mhendriks/DSMR-API-V2/.github/images/v3.1-eindresultaat.jpg

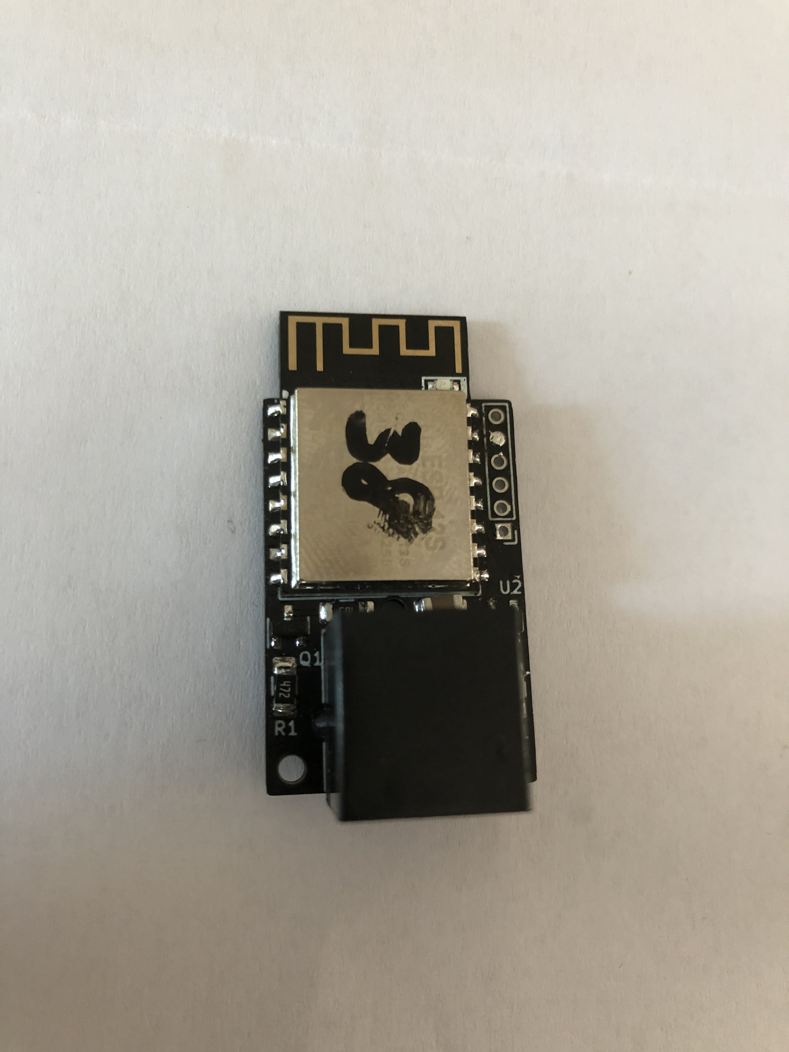
.github/images/v3.1-eindresultaat.jpg
