mhendriks/DSMR-API-V2/.github/images/v3.1-kicad-schema.png

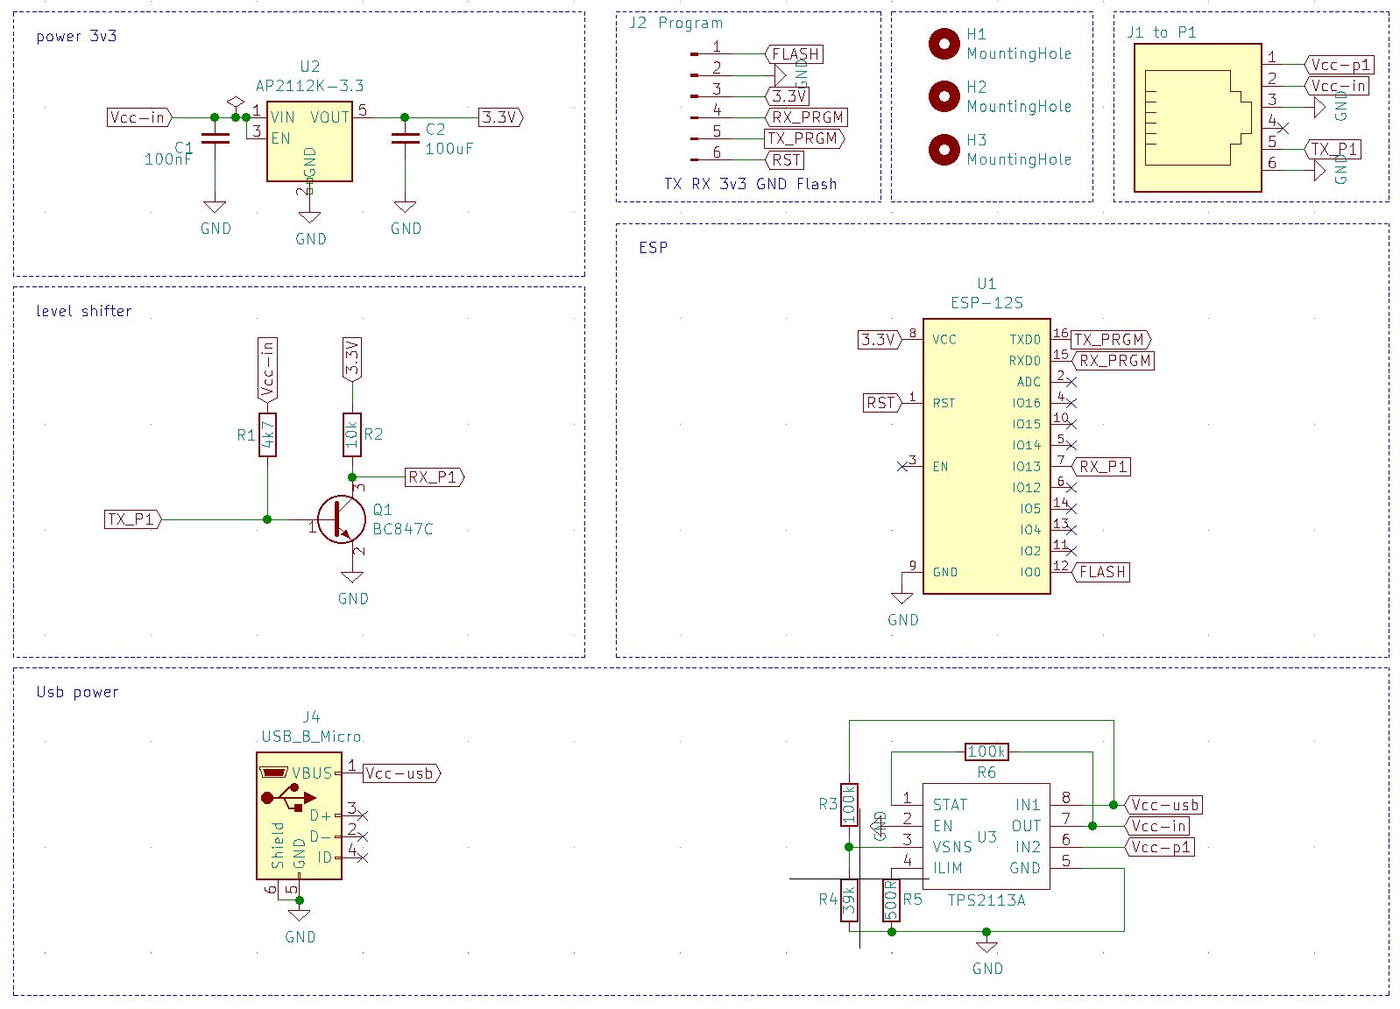
.github/images/v3.1-kicad-schema.png
