mhendriks/DSMR-API-V2/.github/images/v3.3-kicad-schema.png

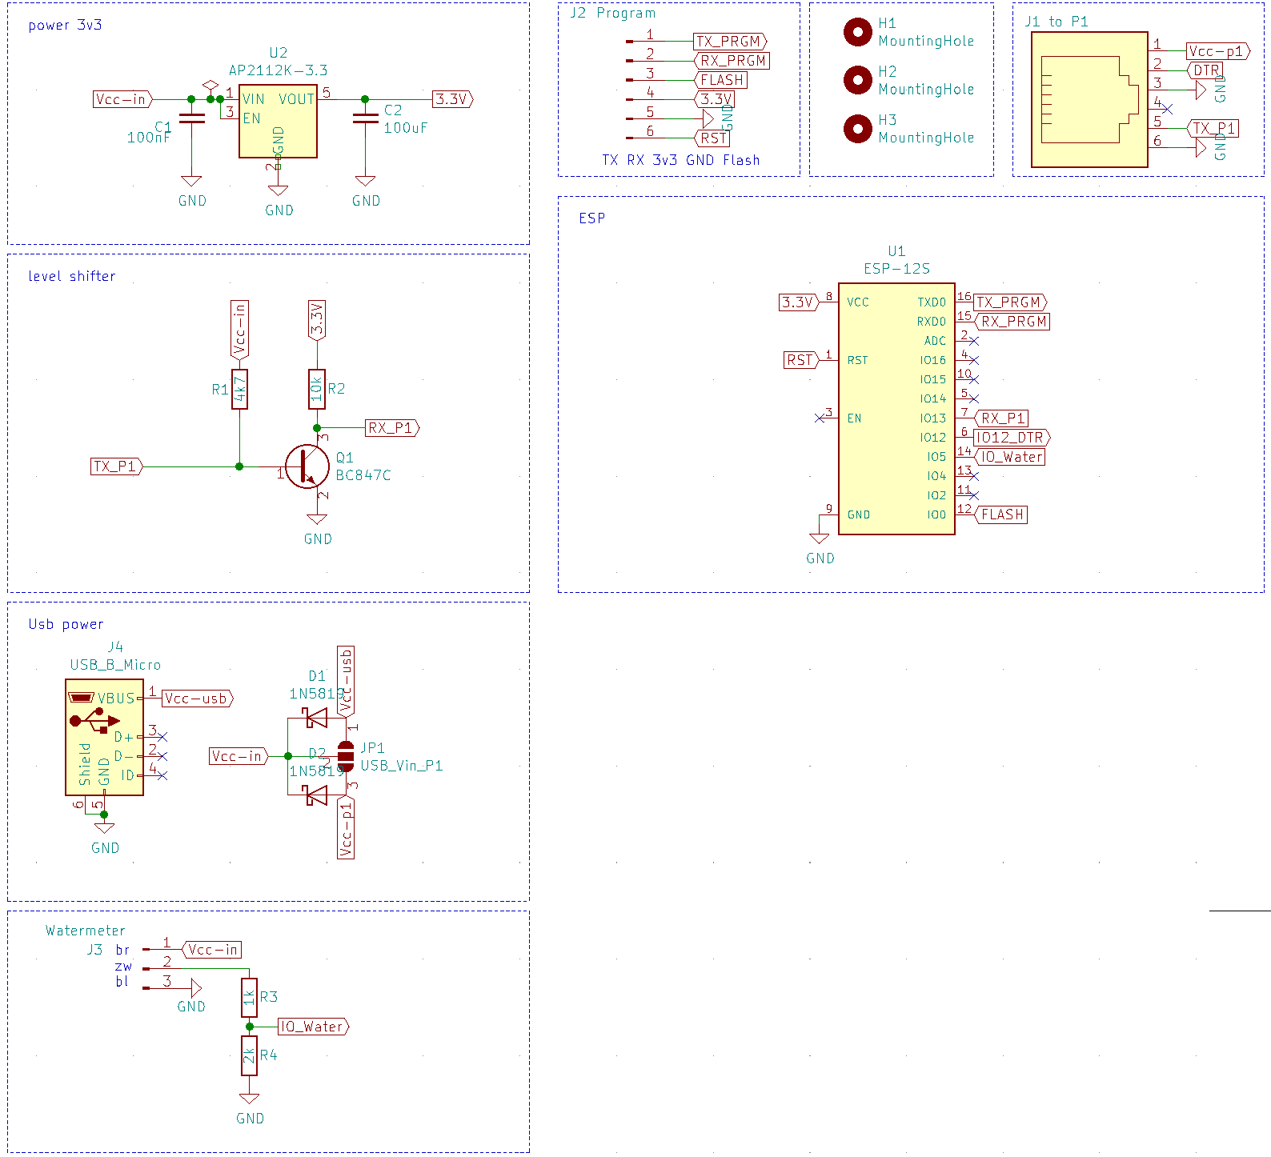
.github/images/v3.3-kicad-schema.png
