mhendriks/DSMR-API-V2/manual/dsmr-api/afb/afbeelding3a.png

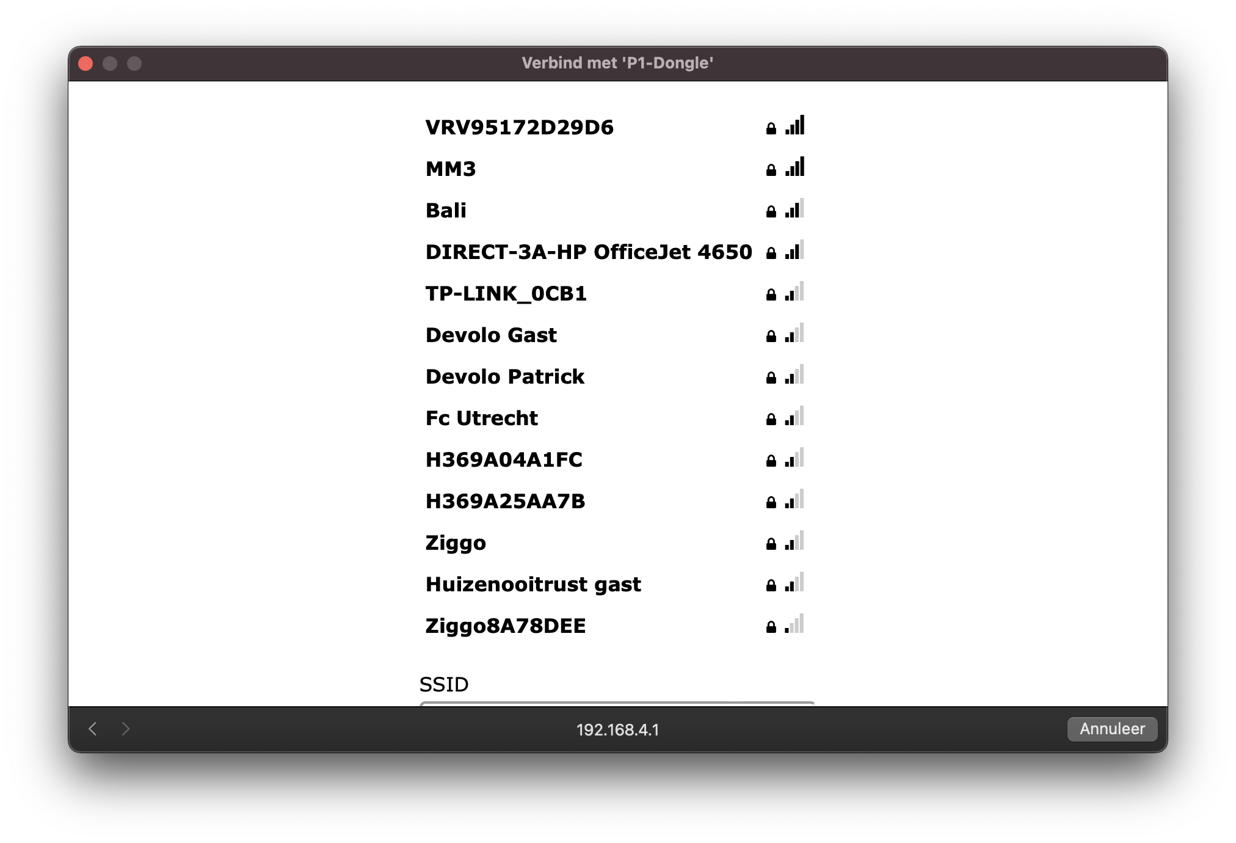
manual/dsmr-api/afb/afbeelding3a.png
