mhendriks/DSMR-API-V2/manual/dsmr-api/afb/check-ip.png

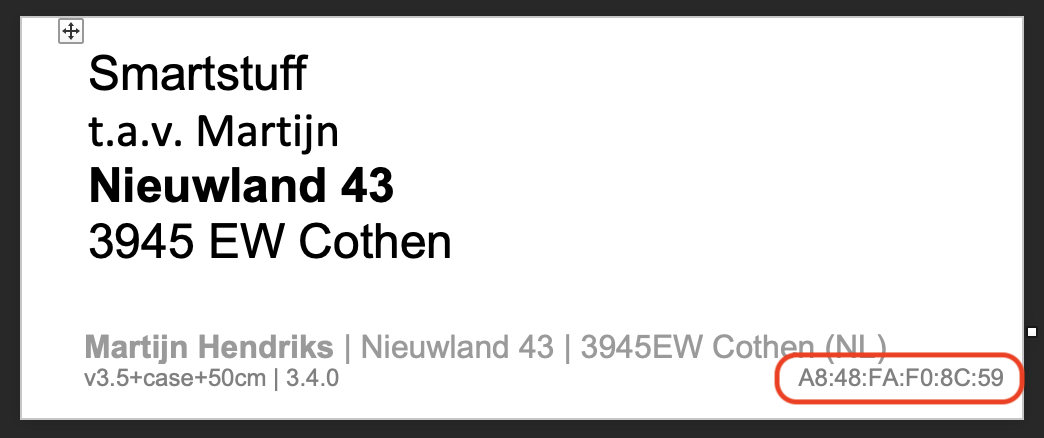
manual/dsmr-api/afb/check-ip.png
