mhendriks/DSMR-API-V2/manual/dsmr-api/Blynk/blynk-app.png

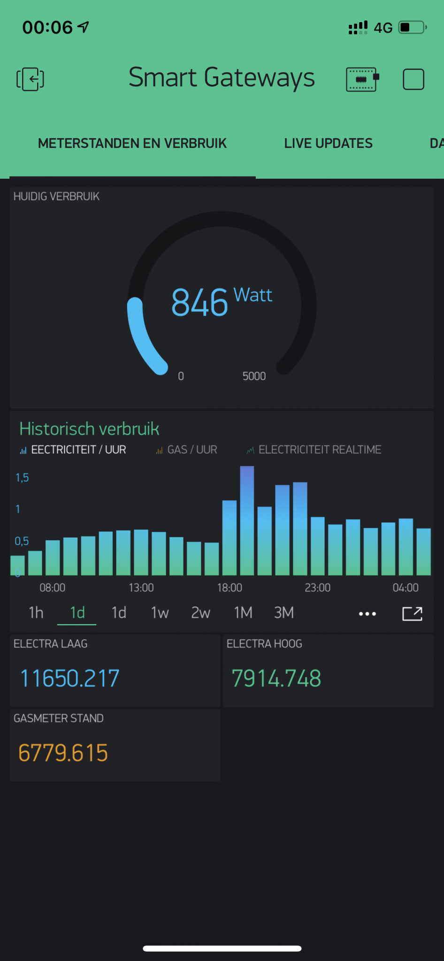
manual/dsmr-api/Blynk/blynk-app.png
