mhendriks/DSMR-API-V2/manual/dsmr-api/watermeter/afb/v4.2-boven.png

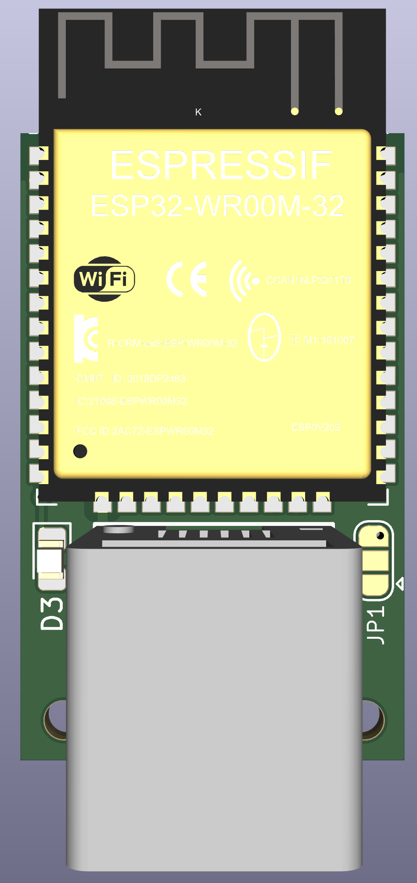
manual/dsmr-api/watermeter/afb/v4.2-boven.png
