mhendriks/DSMR-API-V2/MQTT.ino

/* 
***************************************************************************  
**  Program  : MQTT, part of DSMRloggerAPI
**  Version  : v3.0.0
**
**  Copyright (c) 2021 Willem Aandewiel / Martijn Hendriks  
**
**  TERMS OF USE: MIT License. See bottom of file.                                                            
***************************************************************************      
**  RvdB  changed MQTT stuff to FSM 
**  AaW   simplified and restructured the FSM 
*/

// Declare some variables within global scope

  static IPAddress    MQTTbrokerIP;
  static char         MQTTbrokerIPchar[20];
  int8_t              reconnectAttempts = 0;
  char                lastMQTTtimestamp[15] = "-";
  char                mqttBuff[100];

  enum states_of_MQTT { MQTT_STATE_INIT, MQTT_STATE_TRY_TO_CONNECT, MQTT_STATE_IS_CONNECTED, MQTT_STATE_ERROR };
  enum states_of_MQTT stateMQTT = MQTT_STATE_INIT;

  String            MQTTclientId;

#ifdef HA_DISCOVER
/*

void SendAutoDiscoverHA(const char* dev_name, const char* dev_class, const char* dev_title, const char* dev_unit, const char* dev_payload, const char* state_class, const char* extrapl ){
  char msg_topic[75];
  char msg_payload[500];
  sprintf(msg_topic,"homeassistant/sensor/p1-dongle/%s/config",dev_name);
//    Debugln(msg_topic);

  if (strlen(dev_class)) sprintf(msg_payload,"{\"uniq_id\":\"%s\",\"dev_cla\": \"%s\",\"name\": \"%s\", \"stat_t\": \"%s%s\", \"unit_of_meas\": \"%s\", \"val_tpl\": \"%s\", \"state_class\":\"%s\"%s }", dev_name,dev_class, dev_title, settingMQTTtopTopic, dev_name, dev_unit, dev_payload,state_class, extrapl);
  else sprintf(msg_payload,"{\"uniq_id\":\"%s\",\"name\": \"%s\", \"stat_t\": \"%s%s\", \"unit_of_meas\": \"%s\", \"val_tpl\": \"%s\", \"state_class\":\"%s\"%s }", dev_name, dev_title, settingMQTTtopTopic, dev_name, dev_unit, dev_payload,state_class, extrapl);
//    Debugln(msg_payload);
    if (!MQTTclient.publish(msg_topic, msg_payload, true) ) DebugTf("Error publish(%s) [%s] [%d bytes]\r\n", msg_topic, msg_payload, (strlen(msg_topic) + strlen(msg_payload)));
}

void AutoDiscoverHA(){
//mosquitto_pub -h 192.168.2.250 -p 1883 -t "homeassistant/sensor/power_delivered/config" -m '{"dev_cla": "gas", "name": "Power Delivered", "stat_t": "DSMR-API/power_delivered", "unit_of_meas": "Wh", "val_tpl": "{{ value_json.power_delivered[0].value | round(3) }}" }'

  SendAutoDiscoverHA("timestamp", "", "DSMR Last Update", "", "{{ strptime(value_json.timestamp[0].value[0:12], \'%y%m%d%H%M%S\') }}","measurement", ",\"icon\": \"mdi:clock\"");
  
  SendAutoDiscoverHA("power_delivered", "power", "Power Delivered", "W", "{{ value_json.power_delivered[0].value | round(3) * 1000}}","measurement","");
  SendAutoDiscoverHA("power_returned", "power", "Power Returned", "W", "{{ value_json.power_returned[0].value | round(3) * 1000}}","measurement","");  
  
  SendAutoDiscoverHA("energy_delivered_tariff1", "energy", "Energy Delivered T1", "kWh", "{{ value_json.energy_delivered_tariff1[0].value | round(3) }}","total_increasing","");
  SendAutoDiscoverHA("energy_delivered_tariff2", "energy", "Energy Delivered T2", "kWh", "{{ value_json.energy_delivered_tariff2[0].value | round(3) }}","total_increasing","");
  SendAutoDiscoverHA("energy_returned_tariff1", "energy", "Energy Returned T1", "kWh", "{{ value_json.energy_returned_tariff1[0].value | round(3) }}","total_increasing","");
  SendAutoDiscoverHA("energy_returned_tariff2", "energy", "Energy Returned T2", "kWh", "{{ value_json.energy_returned_tariff2[0].value | round(3) }}","total_increasing","");
  
  SendAutoDiscoverHA("power_delivered_l1", "power", "Power Delivered l1", "W", "{{ value_json.power_delivered_l1[0].value | round(3) * 1000 }}","measurement","");
  SendAutoDiscoverHA("power_delivered_l2", "power", "Power Delivered l2", "W", "{{ value_json.power_delivered_l2[0].value | round(3) * 1000 }}","measurement","");
  SendAutoDiscoverHA("power_delivered_l3", "power", "Power Delivered l3", "W", "{{ value_json.power_delivered_l3[0].value | round(3) * 1000 }}","measurement","");

  SendAutoDiscoverHA("power_returned_l1", "power", "Power Returned l1", "W", "{{ value_json.power_returned_l1[0].value | round(3) * 1000 }}","measurement","");
  SendAutoDiscoverHA("power_returned_l2", "power", "Power Returned l2", "W", "{{ value_json.power_returned_l2[0].value | round(3) * 1000 }}","measurement","");
  SendAutoDiscoverHA("power_returned_l3", "power", "Power Returned l3", "W", "{{ value_json.power_returned_l3[0].value | round(3) * 1000 }}","measurement","");

  SendAutoDiscoverHA("voltage_l1", "voltage", "Voltage l1", "V", "{{ value_json.voltage_l1[0].value | round(0) }}","measurement","");
  SendAutoDiscoverHA("voltage_l2", "voltage", "Voltage l2", "V", "{{ value_json.voltage_l2[0].value | round(0) }}","measurement","");
  SendAutoDiscoverHA("voltage_l3", "voltage", "Voltage l3", "V", "{{ value_json.voltage_l3[0].value | round(0) }}","measurement","");
  
  SendAutoDiscoverHA("current_l1", "current", "Current l1", "A", "{{ value_json.current_l1[0].value | round(0) }}","measurement","");
  SendAutoDiscoverHA("current_l2", "current", "Current l2", "A", "{{ value_json.current_l2[0].value | round(0) }}","measurement","");
  SendAutoDiscoverHA("current_l3", "current", "Current l3", "A", "{{ value_json.current_l3[0].value | round(0) }}","measurement","");

  SendAutoDiscoverHA("gas_delivered", "gas", "Gas Delivered", "m³", "{{ value_json.gas_delivered[0].value | round(2) }}","total_increasing","");
    
}
*/


//--- NEW
String AddPayload(const char* key, const char* value ){
  if ( strlen(value) == 0 ) return "";
  return "\"" + String(key) + "\":\"" + String(value) + "\",";
}

void SendAutoDiscoverHA(const char* dev_name, const char* dev_class, const char* dev_title, const char* dev_unit, const char* dev_payload, const char* state_class, const char* extrapl ){
  char msg_topic[80];
  String msg_payload = "{";
  sprintf(msg_topic,"homeassistant/sensor/p1-dongle/%s/config",dev_name);
//    Debugln(msg_topic);
  msg_payload += AddPayload( "uniq_id"        , dev_name);
  msg_payload += AddPayload( "dev_cla"        , dev_class);
  msg_payload += AddPayload( "name"           , dev_title);
  msg_payload += AddPayload( "stat_t"         , String((String)settingMQTTtopTopic + (String)dev_name).c_str() );
  msg_payload += AddPayload( "unit_of_meas"   , dev_unit);
  msg_payload += AddPayload( "val_tpl"        , dev_payload);
  msg_payload += AddPayload( "stat_cla"       , state_class);
  msg_payload += extrapl;
  msg_payload += "\"dev\":{";
  msg_payload += AddPayload("ids"             , String(WIFI_getChipId()).c_str() );
  msg_payload += AddPayload("name"            , settingHostname);
  msg_payload += "\"mdl\":\"P1 Dongle\",\"mf\":\"Smartstuff\"}}";
//  Debugln(msg_payload);
  if (!MQTTclient.publish(msg_topic, msg_payload.c_str(), true) ) DebugTf("Error publish(%s) [%s] [%d bytes]\r\n", msg_topic, msg_payload, ( strlen(msg_topic) + msg_payload.length() ));
}

void AutoDiscoverHA(){
//mosquitto_pub -h 192.168.2.250 -p 1883 -t "homeassistant/sensor/power_delivered/config" -m '{"dev_cla": "gas", "name": "Power Delivered", "stat_t": "DSMR-API/power_delivered", "unit_of_meas": "Wh", "val_tpl": "{{ value_json.power_delivered[0].value | round(3) }}" }'

  SendAutoDiscoverHA("timestamp", "timestamp", "DSMR Last Update", "", "{{ strptime(value_json.timestamp[0].value[:-1] + '-+0200' if value_json.timestamp[0].value[12] == 'S' else value_json.timestamp[0].value[:-1] + '-+0100', '%y%m%d%H%M%S-%z') }}","", "\"icon\": \"mdi:clock\",");
  SendAutoDiscoverHA("power_delivered", "power", "Power Delivered", "W", "{{ value_json.power_delivered[0].value | round(3) * 1000 }}","measurement","");
  SendAutoDiscoverHA("power_returned" , "power", "Power Returned" , "W", "{{ value_json.power_returned[0].value | round(3) * 1000 }}","measurement","");  
  
  SendAutoDiscoverHA("energy_delivered_tariff1", "energy", "Energy Delivered T1", "kWh", "{{ value_json.energy_delivered_tariff1[0].value | round(3) }}","total_increasing","");
  SendAutoDiscoverHA("energy_delivered_tariff2", "energy", "Energy Delivered T2", "kWh", "{{ value_json.energy_delivered_tariff2[0].value | round(3) }}","total_increasing","");
  SendAutoDiscoverHA("energy_returned_tariff1", "energy", "Energy Returned T1", "kWh", "{{ value_json.energy_returned_tariff1[0].value | round(3) }}","total_increasing","");
  SendAutoDiscoverHA("energy_returned_tariff2", "energy", "Energy Returned T2", "kWh", "{{ value_json.energy_returned_tariff2[0].value | round(3) }}","total_increasing","");
  
  SendAutoDiscoverHA("power_delivered_l1", "power", "Power Delivered l1", "W", "{{ value_json.power_delivered_l1[0].value | round(3) * 1000 }}","measurement","");
  SendAutoDiscoverHA("power_delivered_l2", "power", "Power Delivered l2", "W", "{{ value_json.power_delivered_l2[0].value | round(3) * 1000 }}","measurement","");
  SendAutoDiscoverHA("power_delivered_l3", "power", "Power Delivered l3", "W", "{{ value_json.power_delivered_l3[0].value | round(3) * 1000 }}","measurement","");

  SendAutoDiscoverHA("power_returned_l1", "power", "Power Returned l1", "W", "{{ value_json.power_returned_l1[0].value | round(3) * 1000 }}","measurement","");
  SendAutoDiscoverHA("power_returned_l2", "power", "Power Returned l2", "W", "{{ value_json.power_returned_l2[0].value | round(3) * 1000 }}","measurement","");
  SendAutoDiscoverHA("power_returned_l3", "power", "Power Returned l3", "W", "{{ value_json.power_returned_l3[0].value | round(3) * 1000 }}","measurement","");

  SendAutoDiscoverHA("voltage_l1", "voltage", "Voltage l1", "V", "{{ value_json.voltage_l1[0].value | round(0) }}","measurement","");
  SendAutoDiscoverHA("voltage_l2", "voltage", "Voltage l2", "V", "{{ value_json.voltage_l2[0].value | round(0) }}","measurement","");
  SendAutoDiscoverHA("voltage_l3", "voltage", "Voltage l3", "V", "{{ value_json.voltage_l3[0].value | round(0) }}","measurement","");
  
  SendAutoDiscoverHA("current_l1", "current", "Current l1", "A", "{{ value_json.current_l1[0].value | round(0) }}","measurement","");
  SendAutoDiscoverHA("current_l2", "current", "Current l2", "A", "{{ value_json.current_l2[0].value | round(0) }}","measurement","");
  SendAutoDiscoverHA("current_l3", "current", "Current l3", "A", "{{ value_json.current_l3[0].value | round(0) }}","measurement","");

  SendAutoDiscoverHA("gas_delivered", "gas", "Gas Delivered", "m³", "{{ value_json.gas_delivered[0].value | round(2) }}","total_increasing","");
  
}
#endif

//===========================================================================================
void connectMQTT() 
{
  
  if (Verbose2) DebugTf("MQTTclient.connected(%d), mqttIsConnected[%d], stateMQTT [%d]\r\n", MQTTclient.connected(), mqttIsConnected, stateMQTT);

  if ( (settingMQTTinterval == 0) || (strlen(settingMQTTbroker) < 4) ) {
    mqttIsConnected = false;
    return;
  }
  
  if (!MQTTclient.connected() || stateMQTT != MQTT_STATE_IS_CONNECTED)
  {
    mqttIsConnected = false;
    stateMQTT = MQTT_STATE_INIT;
  }

  mqttIsConnected = connectMQTT_FSM();
  
  if (Verbose1) DebugTf("connected()[%d], mqttIsConnected[%d], stateMQTT [%d]\r\n", MQTTclient.connected(), mqttIsConnected, stateMQTT);

  CHANGE_INTERVAL_SEC(reconnectMQTTtimer, 5);

}

//===========================================================================================

void MQTTcallback(char* topic, byte* payload, unsigned int length) {
  if (length > 24) return;
  for (int i=0;i<length;i++) UpdateVersion[i] = (char)payload[i];
  DebugT(F("Message arrived ["));Debug(topic);Debug("] ");Debugln(UpdateVersion);
  UpdateRequested = true;
}

//===========================================================================================
bool connectMQTT_FSM() 
{  
  switch(stateMQTT) 
  {
    case MQTT_STATE_INIT:  
//          DebugTln(F("MQTT State: MQTT Initializing"));
          LogFile("MQTT State: MQTT Initializing",true);
          WiFi.hostByName(settingMQTTbroker, MQTTbrokerIP);  // lookup the MQTTbroker convert to IP
/*
int n = MDNS.queryService("espserver", "tcp");
 
  if (n == 0)  DebugTln("No MQTT host found");
  else {
    Serial.println("Service found");
    Serial.println("Host: " + String(MDNS.hostname(0)));
    Serial.print("IP  : " );
    Serial.println(MDNS.IP(0));
    Serial.println("Port: " + String(MDNS.port(0)));
  }
*/   
          snprintf(MQTTbrokerIPchar, sizeof(MQTTbrokerIPchar), "%d.%d.%d.%d", MQTTbrokerIP[0]
                                                                            , MQTTbrokerIP[1]
                                                                            , MQTTbrokerIP[2]
                                                                            , MQTTbrokerIP[3]);
          if (!isValidIP(MQTTbrokerIP))  
          {
            DebugTf("ERROR: [%s] => is not a valid URL\r\n", settingMQTTbroker);
            settingMQTTinterval = 0;
            stateMQTT = MQTT_STATE_ERROR;
            return false;
          }
          
          //MQTTclient.disconnect();
          //DebugTf("disconnect -> MQTT status, rc=%d \r\n", MQTTclient.state());
          DebugTf("[%s] => setServer(%s, %d) \r\n", settingMQTTbroker, MQTTbrokerIPchar, settingMQTTbrokerPort);
          MQTTclient.setServer(MQTTbrokerIPchar, settingMQTTbrokerPort);
          DebugTf("setServer  -> MQTT status, rc=%d \r\n", MQTTclient.state());
          MQTTclientId  = String(settingHostname) + "-" + WiFi.macAddress();
          MQTTclient.setCallback(MQTTcallback); //set listner update callback
          stateMQTT = MQTT_STATE_TRY_TO_CONNECT;
          reconnectAttempts = 0;

    case MQTT_STATE_TRY_TO_CONNECT:
          LogFile("MQTT State: MQTT try to connect",true);
          DebugTf("MQTT server is [%s], IP[%s]\r\n", settingMQTTbroker, MQTTbrokerIPchar);
      
          DebugTf("Attempting MQTT connection as [%s] .. \r\n", MQTTclientId.c_str());
          reconnectAttempts++;

          //--- If no username, then anonymous connection to broker, otherwise assume username/password.
          sprintf(cMsg,"%sLWT",settingMQTTtopTopic);
          if (String(settingMQTTuser).length() == 0) 
          {
            DebugT(F("without a Username/Password "));
            MQTTclient.connect(MQTTclientId.c_str(),"","",cMsg,1,true,"Offline");
          } 
          else 
          {
            DebugTf("with Username [%s] and password ", settingMQTTuser);
            MQTTclient.connect(MQTTclientId.c_str(), settingMQTTuser, settingMQTTpasswd,cMsg,1,true,"Offline");
          }
          //--- If connection was made succesful, move on to next state...
          if (MQTTclient.connected())
          {
            reconnectAttempts = 0;  
            Debugf(" .. connected -> MQTT status, rc=%d\r\n", MQTTclient.state());
            MQTTclient.publish(cMsg,"Online", true);
            sprintf(cMsg,"%supdate",settingMQTTtopTopic);
            MQTTclient.setBufferSize(650);
#ifdef HA_DISCOVER
            AutoDiscoverHA();
#endif            
            MQTTclient.subscribe(cMsg); //subscribe mqtt update

            LogFile("MQTT connected",false);
            MQTTclient.loop();
            stateMQTT = MQTT_STATE_IS_CONNECTED;
            return true;
          }
          Debugf(" -> MQTT status, rc=%d \r\n", MQTTclient.state());
      
          //--- After 3 attempts... go wait for a while.
          if (reconnectAttempts >= 3)
          {
            DebugTln(F("3 attempts have failed. Retry wait for next reconnect in 5 secs\r"));
            stateMQTT = MQTT_STATE_ERROR;  // if the re-connect did not work, then return to wait for reconnect
            DebugTln(F("Next State: MQTT_STATE_ERROR"));
          }   
          break;
          
    case MQTT_STATE_IS_CONNECTED:
          LogFile("MQTT Connected",false);
          MQTTclient.loop();
          return true;

    case MQTT_STATE_ERROR:
          LogFile("MQTT Error: retry in 5 seconds",true);

          //--- next retry in 5 sec.
          CHANGE_INTERVAL_SEC(reconnectMQTTtimer, 5);
          break;

    default:
          DebugTln(F("MQTT State: default, this should NEVER happen!"));
          //--- do nothing, this state should not happen
          stateMQTT = MQTT_STATE_INIT;
          CHANGE_INTERVAL_SEC(reconnectMQTTtimer, 5);
          DebugTln(F("Next State: MQTT_STATE_INIT"));
          break;
  }

  return false;  

} // connectMQTT_FSM()

//=======================================================================
void MQTTsendGas(){

  if (gasDelivered){
    sprintf(cMsg,"%s%s",settingMQTTtopTopic,"gas_delivered");
    char msg[60];
    sprintf(msg,"{\"gas_delivered\":[{\"value\":%.3f,\"unit\":\"m3\"}]}",gasDelivered);
    if (!MQTTclient.publish(cMsg, msg) ) DebugTf("Error publish(%s) [%s] [%d bytes]\r\n", cMsg, msg, (strlen(cMsg) + strlen(msg)));
  }
}

//=======================================================================
void MQTTsendWater(){

  if (waterDelivered){
    sprintf(cMsg,"%s%s",settingMQTTtopTopic,"water_delivered");
    char msg[60];
    sprintf(msg,"{\"water_delivered\":[{\"value\":%.3f,\"unit\":\"m3\"}]}",waterDelivered);
    if (!MQTTclient.publish(cMsg, msg) ) DebugTf("Error publish(%s) [%s] [%d bytes]\r\n", cMsg, msg, (strlen(cMsg) + strlen(msg)));
  }
}
//=======================================================================

struct buildJsonMQTT {
/* twee types
 *  {energy_delivered_tariff1":[{"value":11741.29,"unit":"kWh"}]}"
 *  {equipment_id":[{"value":"4530303435303033383833343439383137"}]}"
 *  
 *  msg = "{\""+Name+"\":[{\"value\":"+value_to_json(i.val())+",\"unit\":"+Unit+"}]}";
 *  msg = "\"{\""+Name+"\":[{\"value\":"+value_to_json(i.val())+"}]}\""
 *  
 */
     char msg[256];  
    template<typename Item>
    void apply(Item &i) {
      char Name[25];
      strncpy(Name,String(Item::name).c_str(),sizeof(Name));
      if ( !isInFieldsArray(Name) ) {
      if ( i.present() ) {
//          if (Name == "mbus1_delivered") Name = "gas_delivered";    
          snprintf(cMsg, 150, "%s%s",settingMQTTtopTopic,Name);
          if (strlen(Item::unit()) > 0) snprintf(msg, sizeof(msg), "{\"%s\":[{\"value\":%s,\"unit\":\"%s\"}]}", Name, String(value_to_json(i.val())).c_str(), Item::unit() );
          else snprintf(msg, sizeof(msg), "{\"%s\":[{\"value\":%s}]}", Name, String(value_to_json(i.val())).c_str() ); 
//          if (Verbose2) DebugTln("mqtt bericht: "+msg);
            MQTTclient.publish( cMsg, msg );
//          if ( !MQTTclient.publish( cMsg, msg ) ) DebugTf("Error publish(%s) [%s] [%d bytes]\r\n", cMsg, msg, strlen(cMsg) + strlen(msg) );          
//          if (strlen(Item::unit()) > 0) msg = "{\""+String(Name)+"\":[{\"value\":"+value_to_json(i.val())+",\"unit\":\""+Item::unit()+"\"}]}";
//          else msg = "{\""+String(Name)+"\":[{\"value\":"+value_to_json(i.val())+"}]}";
      } else {
        //not present
#ifdef NO_HIST        
          if ( strcmp(Name,"current_l2") == 0 or strcmp(Name,"current_l3") == 0 
               or strcmp(Name,"power_delivered_l2") == 0 or strcmp(Name,"power_delivered_l3") == 0 
               or strcmp(Name,"power_returned_l2") == 0 or strcmp(Name,"power_returned_l3") == 0 
               or strcmp(Name,"voltage_l2") == 0 or strcmp(Name,"voltage_l3") == 0
             ) {
            snprintf(cMsg, 150, "%s%s",settingMQTTtopTopic,Name);
            if (strlen(Item::unit()) > 0) snprintf(msg, sizeof(msg), "{\"%s\":[{\"value\":%s,\"unit\":\"%s\"}]}", Name, String(value_to_json(i.val())).c_str(), Item::unit() );
            else snprintf(msg, sizeof(msg), "{\"%s\":[{\"value\":%s}]}", Name, String(value_to_json(i.val())).c_str() ); 
//          if (Verbose2) DebugTln("mqtt bericht: "+msg);
            MQTTclient.publish( cMsg, msg );
//          if ( !MQTTclient.publish( cMsg, msg ) ) DebugTf("Error publish(%s) [%s] [%d bytes]\r\n", cMsg, msg, strlen(cMsg) + strlen(msg) );

          }
#endif        
        }// else i.present() 

      } // if isInFieldsArray
  } //apply
  
  template<typename Item>
  Item& value_to_json(Item& i) {
    return i;
  }

  String value_to_json( String i ){
    return "\"" + i + "\"";
  }
  
  double value_to_json(FixedValue i) {
    return i.int_val()/1000.0;
  }

  double value_to_json(TimestampedFixedValue i) {
    return i;
  }

}; // buildJsonMQTT

//===========================================================================================
void MQTTSend(const char* item, String value){
  String msg = "{\"" + String(item) + "\":[{\"value\":\""+ value + "\"}]}";
  sprintf(cMsg,"%s%s", settingMQTTtopTopic,item);
  if (!MQTTclient.publish(cMsg, (byte*)msg.c_str(),msg.length(),true ) ) {
    DebugTf("Error publish (%s) [%s] [%d bytes]\r\n", cMsg, msg.c_str(), (strlen(cMsg) + msg.length()));
    StaticInfoSend = false; //probeer het later nog een keer
  }
}

void MQTTSend(const char* item, int32_t value){
  String msg = "{\"" + String(item) + "\":[{\"value\":"+ value + "}]}";
  sprintf(cMsg,"%s%s", settingMQTTtopTopic,item);
  if (!MQTTclient.publish(cMsg, (byte*)msg.c_str(),msg.length(),true ) ) {
    DebugTf("Error publish (%s) [%s] [%d bytes]\r\n", cMsg, msg.c_str(), (strlen(cMsg) + msg.length()));
    StaticInfoSend = false; //probeer het later nog een keer
  }
}
//===========================================================================================
void MQTTSentStaticInfo(){
  if ((settingMQTTinterval == 0) || (strlen(settingMQTTbroker) < 4) ) return;
  StaticInfoSend = true;
  MQTTSend("identification",DSMRdata.identification);
  MQTTSend("p1_version",DSMRdata.p1_version);
  MQTTSend("equipment_id",DSMRdata.equipment_id);
  MQTTSend("firmware",_VERSION_ONLY);
  MQTTSend("ip_address",WiFi.localIP().toString());
  MQTTSend( "wifi_rssi",WiFi.RSSI() );
  if (DSMRdata.mbus1_device_type_present){ MQTTSend("gas_device_type", (uint32_t)DSMRdata.mbus1_device_type ); }
  if (DSMRdata.mbus1_equipment_id_tc_present){ MQTTSend("gas_equipment_id",DSMRdata.mbus1_equipment_id_tc); }
  MQTTSend( "highest_peak_pwr", String(DSMRdata.highest_peak_pwr.val(), 3) );
  MQTTSend( "highest_peak_pwr_13mnd", DSMRdata.highest_peak_pwr_13mnd );
  
}
//===========================================================================================
void sendMQTTData() 
{
  if ((settingMQTTinterval == 0) || (strlen(settingMQTTbroker) < 4) || bailout() ) return;

  //make proper TopTopic
  if (settingMQTTtopTopic[strlen(settingMQTTtopTopic)-1] != '/') snprintf(settingMQTTtopTopic, sizeof(settingMQTTtopTopic), "%s/",  settingMQTTtopTopic);

  if (MQTTclient.connected() && !mqttIsConnected) {
    sprintf(cMsg,"%sLWT",settingMQTTtopTopic);
    MQTTclient.publish(cMsg,"Offline", true); //LWT status update
    MQTTclient.disconnect(); //disconnect when connection is not allowed
  }

  if (!MQTTclient.connected() || !mqttIsConnected) DebugTf("MQTTclient.connected(%d), mqttIsConnected[%d], stateMQTT [%d]\r\n", MQTTclient.connected(), mqttIsConnected, stateMQTT);
  
  if (!MQTTclient.connected())  
  {
    if ( DUE( reconnectMQTTtimer) || mqttIsConnected)
    {
      mqttIsConnected = false;
      StaticInfoSend = false; //zorg voor resend retained info
      connectMQTT();
      return; //verlaat verzending
    }
    else
    {
      DebugTf("trying to reconnect in less than %d seconds\r\n", (TIME_LEFT_SEC(reconnectMQTTtimer) +1) );
    }
    if ( !mqttIsConnected ) 
    {
      DebugTln(F("no connection with a MQTT broker .."));
      return;
    }
  }

  DebugTf("Sending data to MQTT server [%s]:[%d]\r\n", settingMQTTbroker, settingMQTTbrokerPort);
  if ((telegramCount - telegramErrors) > 2 && !StaticInfoSend){
    MQTTSentStaticInfo();
  }
  fieldsElements = INFOELEMENTS;
  DSMRdata.applyEach(buildJsonMQTT()); 
  
  MQTTsendGas();
  MQTTsendWater();

} // sendMQTTData()

/***************************************************************************
*
* Permission is hereby granted, free of charge, to any person obtaining a
* copy of this software and associated documentation files (the
* "Software"), to deal in the Software without restriction, including
* without limitation the rights to use, copy, modify, merge, publish,
* distribute, sublicense, and/or sell copies of the Software, and to permit
* persons to whom the Software is furnished to do so, subject to the
* following conditions:
*
* The above copyright notice and this permission notice shall be included
* in all copies or substantial portions of the Software.
*
* THE SOFTWARE IS PROVIDED "AS IS", WITHOUT WARRANTY OF ANY KIND, EXPRESS
* OR IMPLIED, INCLUDING BUT NOT LIMITED TO THE WARRANTIES OF
* MERCHANTABILITY, FITNESS FOR A PARTICULAR PURPOSE AND NONINFRINGEMENT.
* IN NO EVENT SHALL THE AUTHORS OR COPYRIGHT HOLDERS BE LIABLE FOR ANY
* CLAIM, DAMAGES OR OTHER LIABILITY, WHETHER IN AN ACTION OF CONTRACT, TORT
* OR OTHERWISE, ARISING FROM, OUT OF OR IN CONNECTION WITH THE SOFTWARE OR
* THE USE OR OTHER DEALINGS IN THE SOFTWARE.
* 
****************************************************************************
*/
