mhendriks/DSMR-API-V2/version.h

//The version number conforms to semver.org format
#define _VERSION_MAJOR 3
#define _VERSION_MINOR 5
#define _VERSION_PATCH 10
#define _VERSION_BUILD 1291
#define _VERSION_DATE "09/09/2023"
#define _VERSION_TIME "08:12:30"
#define _VERSION_ONLY "3.5.10"
#define _VERSION_NOBUILD "3.5.10 (09/09/2023)"
#define _VERSION "3.5.10+1291 (09/09/2023)"
//The version information is created automatically, more information here: https://github.com/rvdbreemen/autoinc-semver
